4pplet/waffling60/readme-images/waffling60-ALPS_Rev_C1_Tray.png

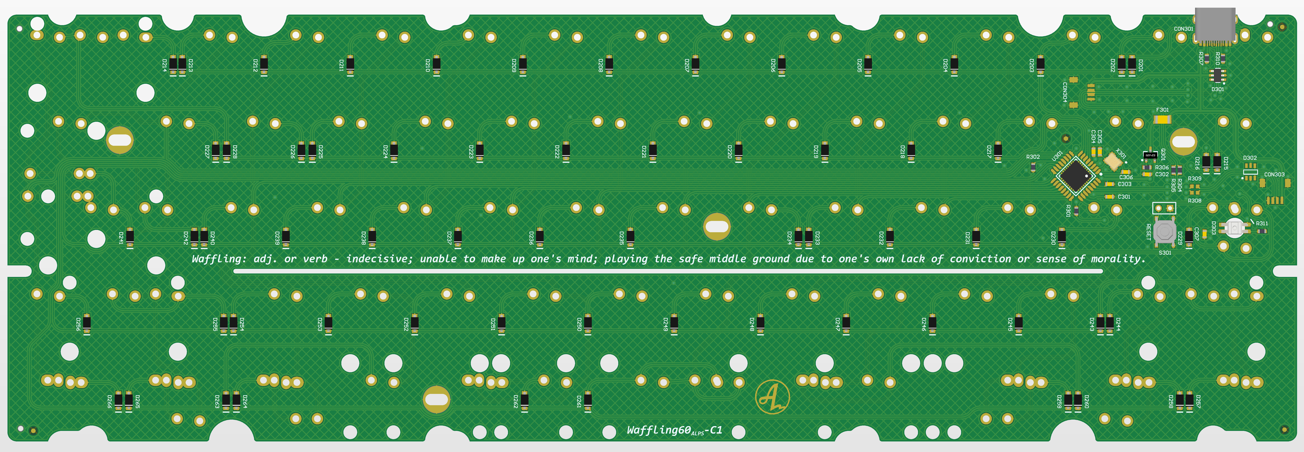
readme-images/waffling60-ALPS_Rev_C1_Tray.png
