4pplet/waffling60/readme-images/waffling60-BK_Rev_B4.jpg

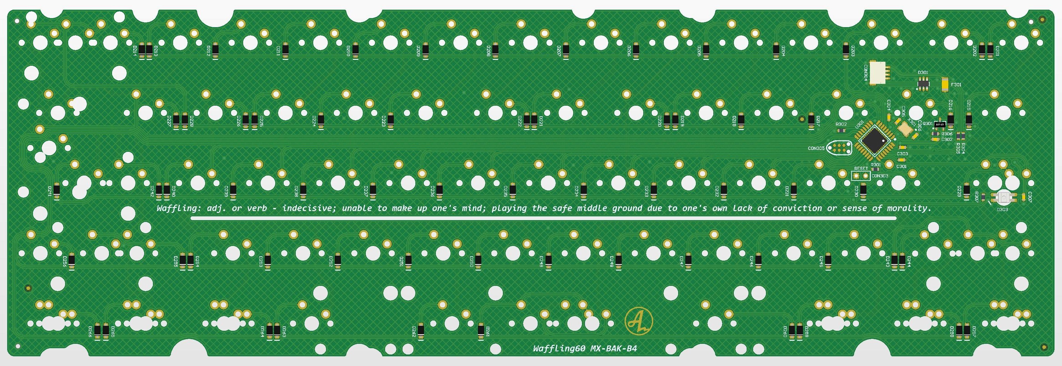
readme-images/waffling60-BK_Rev_B4.jpg
