4pplet/waffling60/readme-images/waffling60-SE_Rev_B2.jpg

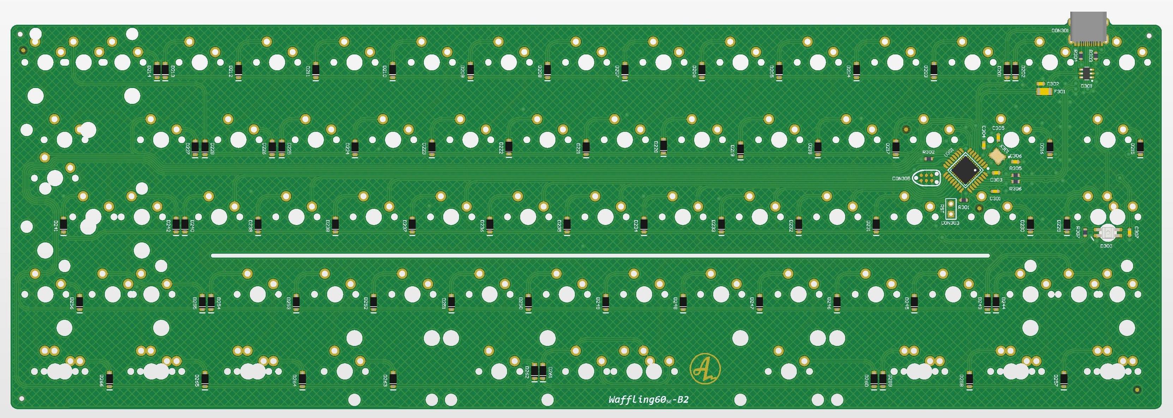
readme-images/waffling60-SE_Rev_B2.jpg
