4pplet/waffling60/readme-images/waffling60HS_Rev_B3.jpg

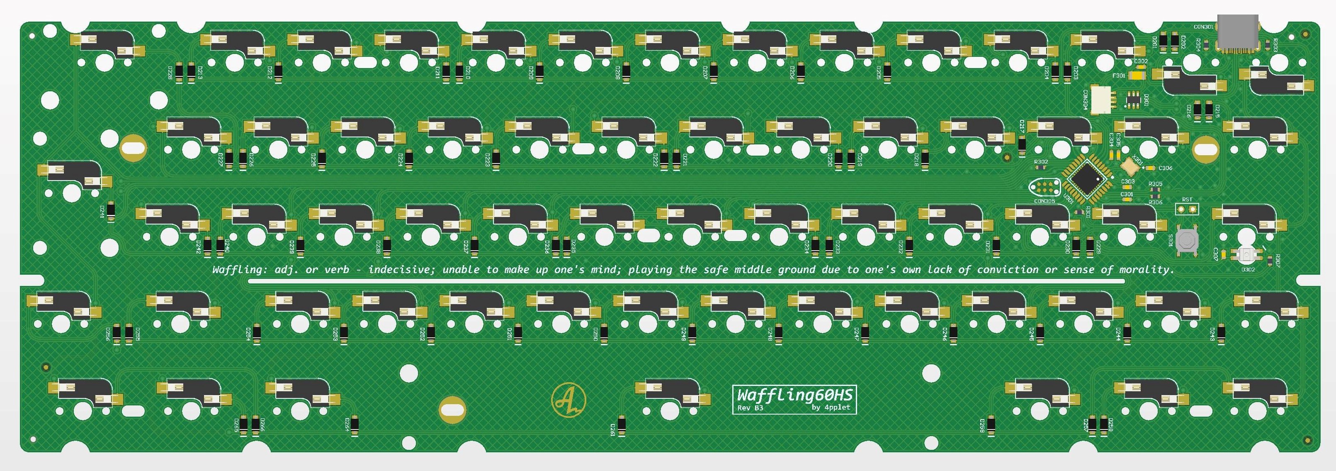
readme-images/waffling60HS_Rev_B3.jpg
